JolonB/SDI12-UART/hardware/config_1/schem/config_1/config_1.kicad_pcb

## KiCad design board/afdDriver/afdDriver.kicad_pcb

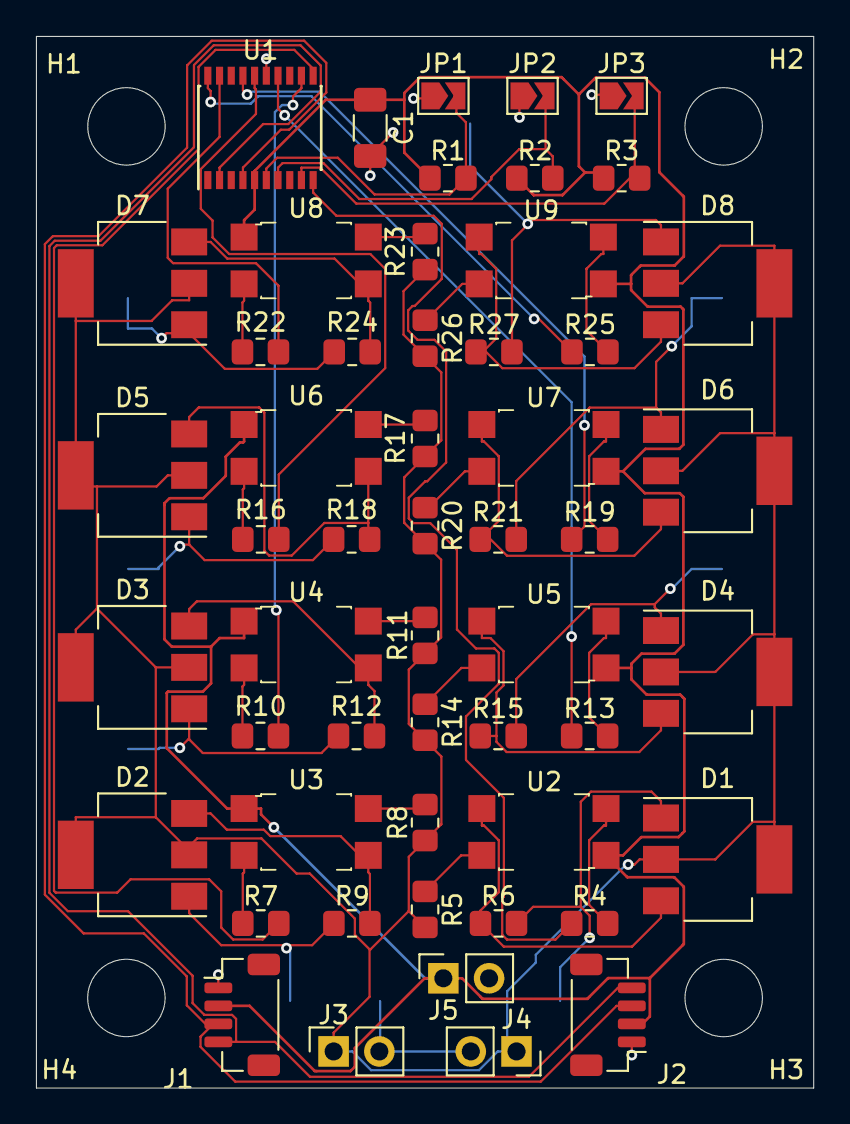
[picture p10: board afdDriver.kicad_pcb from above]

Board: 2 copper layers, 43.2 x 58.4 mm, 58 parts (1 on the bottom side), 49 nets.

Parts:
C1: 0.1 uFd; C_1206_3216Metric_Pad1.33x1.80mm_HandSolder
D1, D2, D3, D4, D5, D6, D7, D8: Z0103MN; SOT-223
DS1: IEL-O-VI_C63.396.208-02_SMD; C63.396.208-02_SMD
H1, H2, H3, H4: MountingHole; MountingHole_4.3mm_M4_ISO14580
J1, J2: Qwiic_Connector; JST_SH_BM04B-SRSS-TB_1x04-1MP_P1.00mm_Vertical
J3, J4: HighVoltageAC; PinSocket_1x02_P2.54mm_Vertical
J5: Power; PinSocket_1x02_P2.54mm_Vertical
JP1: ADDR0; SolderJumper-2_P1.3mm_Open_TrianglePad1.0x1.5mm
JP2: ADDR1; SolderJumper-2_P1.3mm_Open_TrianglePad1.0x1.5mm
JP3: ADDR2; SolderJumper-2_P1.3mm_Open_TrianglePad1.0x1.5mm
R1, R2, R3: 10K Ohm; R_0805_2012Metric_Pad1.20x1.40mm_HandSolder
R4, R5, R6, R7, R8, R9, R10, R11, R12, R13, R14, R15, R16, R17, R18, R19, R20, R21, R22, R23, R24, R25, R26, R27: 390; R_0805_2012Metric_Pad1.20x1.40mm_HandSolder
U1: PCF8574TS; SSOP-20_4.4x6.5mm_P0.65mm
U2, U3, U4, U5, U6, U7, U8, U9: QTM3063T1; 4-SMD_3.8x4.6mm

Connections:
+5V: C1.1, J1.2, J2.2, J5.1, R1.1, R2.1, R3.1, U1.5, U2.1, U3.1, U4.1, U5.1, U6.1, U7.1, U8.1, U9.1
/A0: JP1.2, R1.2, U1.6
/A1: JP2.2, R2.2, U1.7
/A2: JP3.2, R3.2, U1.9
/EnbSegA: R4.2, U1.10
/EnbSegB: R7.2, U1.11
/EnbSegC: R10.2, U1.12
/EnbSegD: R13.2, U1.14
/EnbSegE: R16.2, U1.16
/EnbSegF: R19.2, U1.17
/EnbSegG: R22.2, U1.19
/EnbSegH: R25.2, U1.20
/SCL: J1.4, J2.4, U1.2
/SDA: J1.3, J2.3, U1.4
/SegA: D1.1, DS1.2, R6.1
/SegB: D2.1, DS1.3, R9.1
/SegC: D3.1, DS1.7, R12.1
/SegD: D4.1, DS1.8, R15.1
/SegE: D5.1, DS1.11, R18.1
/SegF: D6.1, DS1.14, R21.1
/SegG: D7.1, DS1.17, R24.1
/SegH: D8.1, DS1.20, R27.1
GND: C1.2, J1.1, J2.1, J5.2, JP1.1, JP2.1, JP3.1, U1.15
GND1: DS1.1, J3.2, J4.2
HV_AC: D1.2, D1.4, D2.2, D2.4, D3.2, D3.4, D4.2, D4.4, D5.2, D5.4, D6.2, D6.4, D7.2, D7.4, D8.2, D8.4, J3.1, J4.1, R5.1, R8.1, R11.1, R14.1, R17.1, R20.1, R23.1, R26.1
unnamed: D1.3, R6.2, U2.3
unnamed: D2.3, R9.2, U3.3
unnamed: D3.3, R12.2, U4.3
unnamed: D4.3, R15.2, U5.3
unnamed: D5.3, R18.2, U6.3
unnamed: D6.3, R21.2, U7.3
unnamed: D7.3, R24.2, U8.3
unnamed: D8.3, R27.2, U9.3
unnamed: R4.1, U2.2
unnamed: R5.2, U2.4
unnamed: R7.1, U3.2
unnamed: R8.2, U3.4
unnamed: R10.1, U4.2
unnamed: R11.2, U4.4
unnamed: R13.1, U5.2
unnamed: R14.2, U5.4
unnamed: R16.1, U6.2
unnamed: R17.2, U6.4
unnamed: R19.1, U7.2
unnamed: R20.2, U7.4
unnamed: R22.1, U8.2
unnamed: R23.2, U8.4
unnamed: R25.1, U9.2
unnamed: R26.2, U9.4
