JolonB/SDI12-UART/hardware/config_1/schem/config_1/config_1.kicad_pcb

## KiCad design board/afd/afd.kicad_pcb

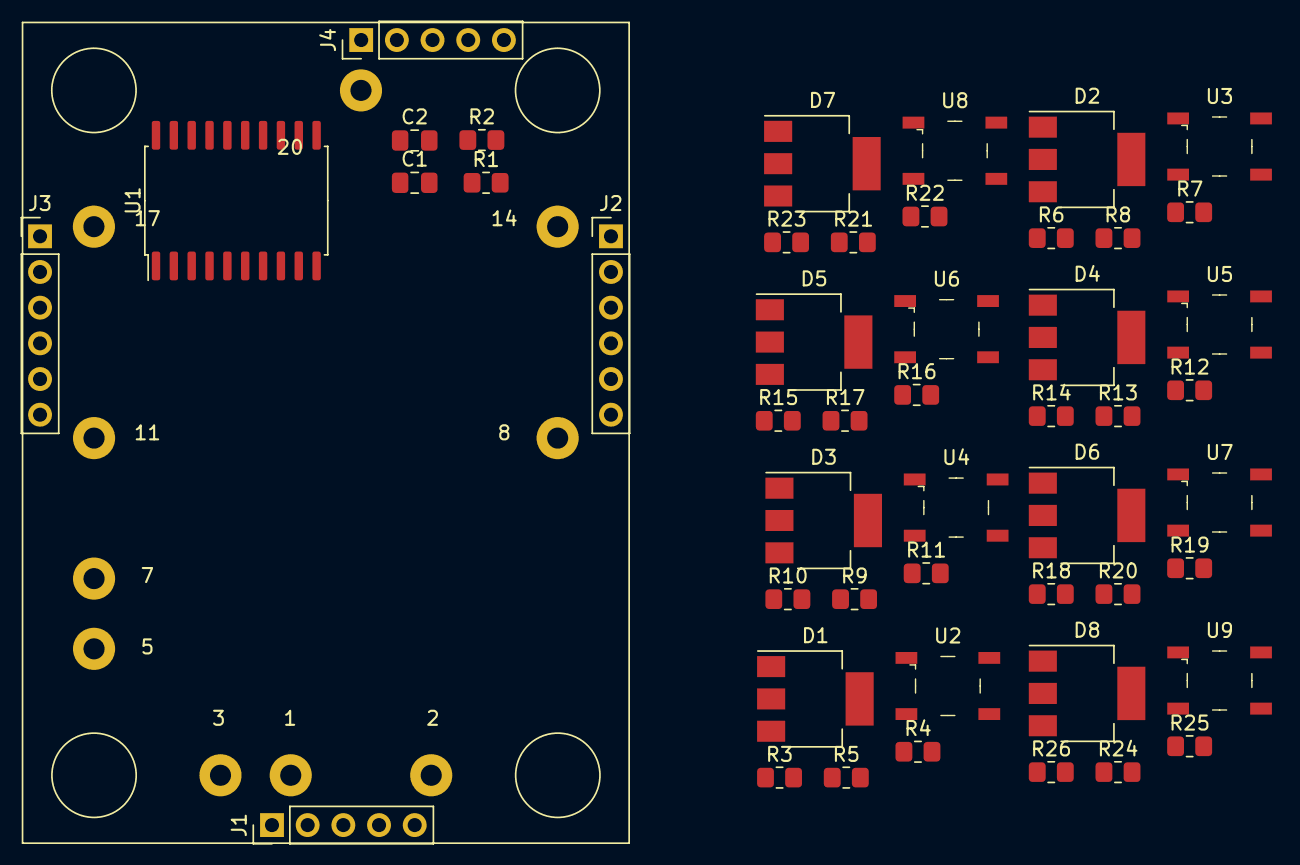
[picture p11: board afd.kicad_pcb from above]

Board: 2 copper layers, 50 parts (0 on the bottom side), 48 nets, no tracks yet.

Parts:
C1, C2: 0.1 uF 20V ceramic; C_0805_2012Metric_Pad1.18x1.45mm_HandSolder
D1, D2, D3, D4, D5, D6, D7, D8: Z0103MN; SOT-223
DS1: IEL-O-VI_C63.396.208-02; C63.396.208-02
J1: ICSP Connector; PinHeader_1x05_P2.54mm_Vertical
J2: Input Connector; PinHeader_1x06_P2.54mm_Vertical
J3: Output Connector; PinHeader_1x06_P2.54mm_Vertical
J4: GPIO Connector; PinHeader_1x05_P2.54mm_Vertical
R1: 10 Kohm; R_0805_2012Metric_Pad1.20x1.40mm_HandSolder
R2: 470 ohm; R_0805_2012Metric_Pad1.20x1.40mm_HandSolder
R3, R4, R5, R6, R7, R8, R9, R10, R11, R12, R13, R14, R15, R16, R17, R18, R19, R20, R21, R22, R23, R24, R25, R26: 390; R_0805_2012Metric_Pad1.20x1.40mm_HandSolder
U1: PIC18F16Q40-E_SO; SOIC-20W_7.5x12.8mm_P1.27mm
U2, U3, U4, U5, U6, U7, U8, U9: MOC3063; SMD-4_5x4.4mm_P4mm

Connections:
+3V3: C2.1, J1.2, J2.5, J3.5, R1.1, U1.1
/EnbSegA: U1.16, U2.1
/EnbSegB: U1.15, U3.1
/EnbSegC: U1.14, U4.1
/EnbSegD: U1.7, U5.1
/EnbSegE: U1.6, U6.1
/EnbSegF: U1.5, U7.1
/EnbSegG: U1.8, U8.1
/EnbSegH: U1.9, U9.1
/GPIO0: J4.5, U1.17
/GPIO1: J4.4, U1.2
/GPIO2: J4.3, U1.3
/GPIO3: J4.2, U1.11
/GPIO4: J4.1, U1.10
/ICSPCLK: J1.5, U1.18
/ICSPDAT: J1.4, U1.19
/MCLR: R2.1, U1.4
/RX1: J2.3, U1.12
/SegA: D1.1, DS1.2, R5.1
/SegB: D2.1, DS1.3, R8.1
/SegC: D3.1, DS1.7, R11.1
/SegD: D4.1, DS1.8, R14.1
/SegE: D5.1, DS1.11, R17.1
/SegF: D6.1, DS1.14, R20.1
/SegG: D7.1, DS1.17, R23.1
/SegH: D8.1, DS1.20, R26.1
/TX1: J3.3, U1.13
/Vpp: C1.1, J1.1, R1.2, R2.2
GND: C1.2, C2.2, J1.3, J2.6, J3.6, U1.20
GND1: DS1.1, J2.4, J3.4, R3.2, R6.2, R9.2, R12.2, R15.2, R18.2, R21.2, R24.2
HV_AC: D1.2, D1.4, D2.2, D2.4, D3.2, D3.4, D4.2, D4.4, D5.2, D5.4, D6.2, D6.4, D7.2, D7.4, D8.2, D8.4, J2.2, J3.2, R4.1, R7.1, R10.1, R13.1, R16.1, R19.1, R22.1, R25.1
unnamed: D1.3, R5.2, U2.4
unnamed: D2.3, R8.2, U3.4
unnamed: D3.3, R11.2, U4.4
unnamed: D4.3, R14.2, U5.4
unnamed: D5.3, R17.2, U6.4
unnamed: D6.3, R20.2, U7.4
unnamed: D7.3, R23.2, U8.4
unnamed: D8.3, R26.2, U9.4
unnamed: J2.1, J3.1
unnamed: R3.1, U2.2
unnamed: R6.1, U3.2
unnamed: R9.1, U4.2
unnamed: R12.1, U5.2
unnamed: R15.1, U6.2
unnamed: R18.1, U7.2
unnamed: R21.1, U8.2
unnamed: R24.1, U9.2
